rheslip/2HPico-Eurorack-Module-Hardware/Images/IMG_0591.JPG

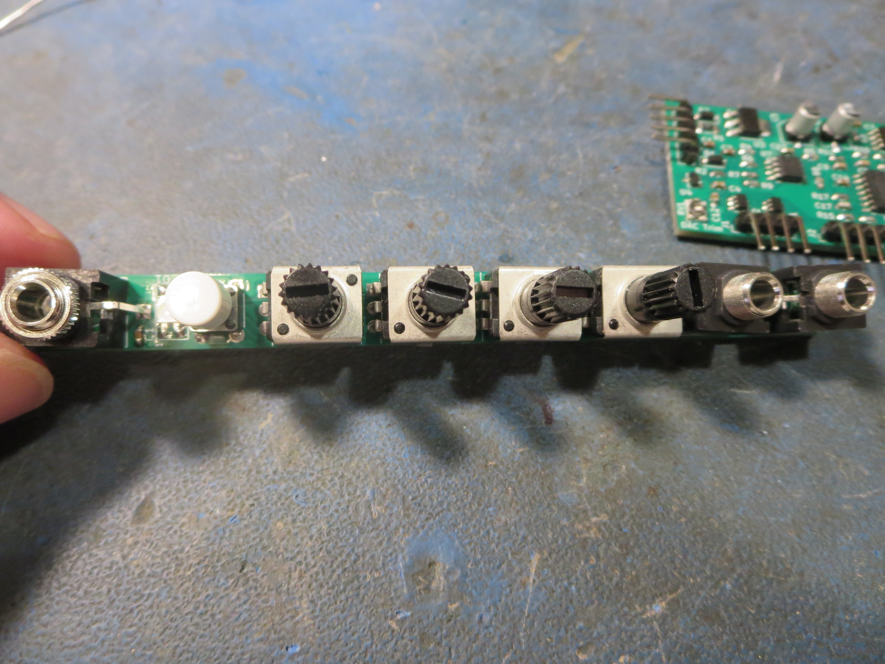
Images/IMG_0591.JPG
