rheslip/2HPico-Eurorack-Module-Hardware/Images/IMG_0592.JPG

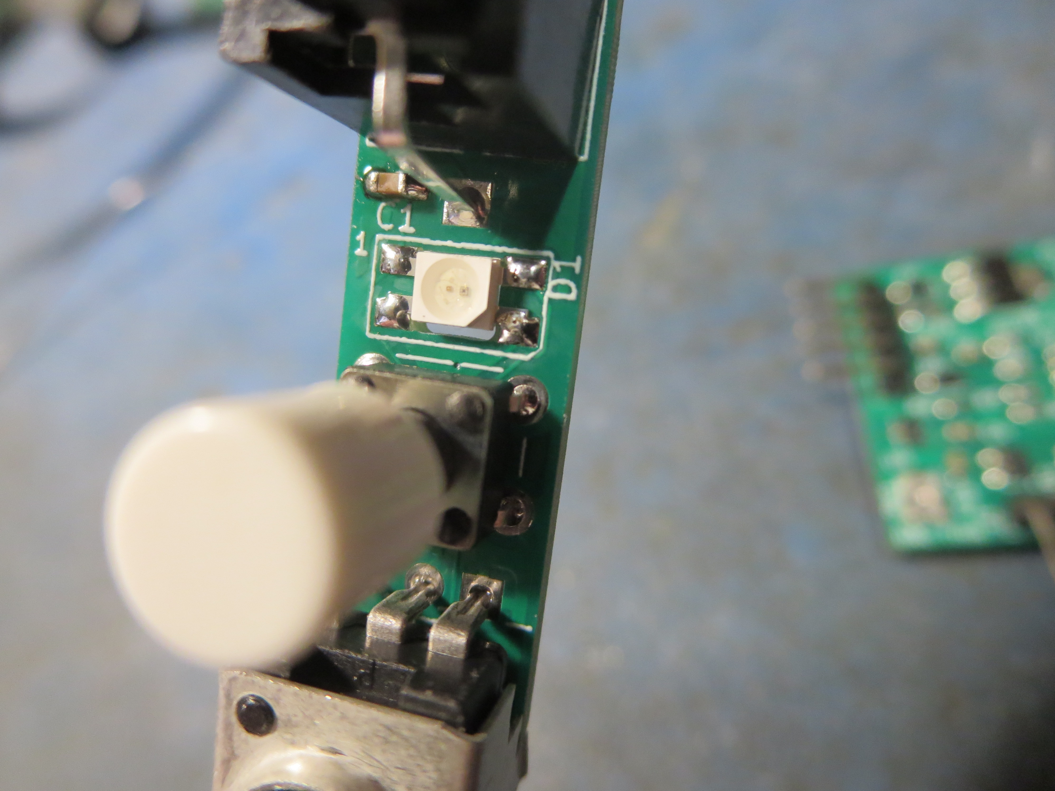
Images/IMG_0592.JPG
