rheslip/2HPico-Eurorack-Module-Hardware/Images/IMG_0594.JPG

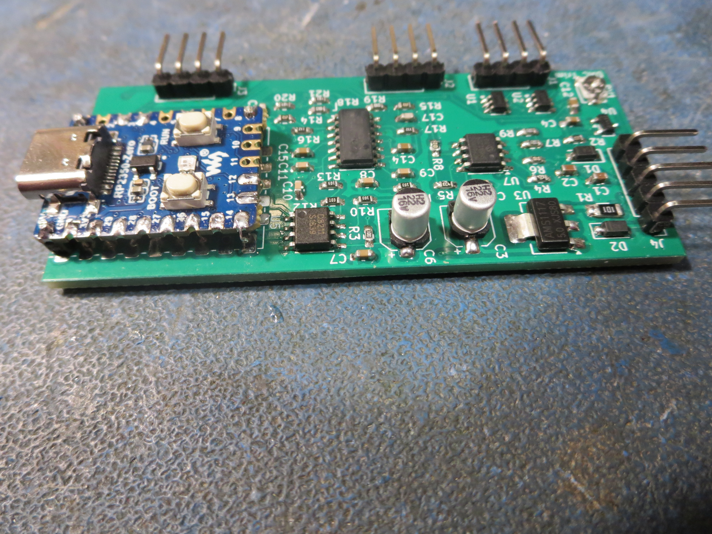
Images/IMG_0594.JPG
