rheslip/2HPico-Eurorack-Module-Hardware/Images/IMG_0597.JPG

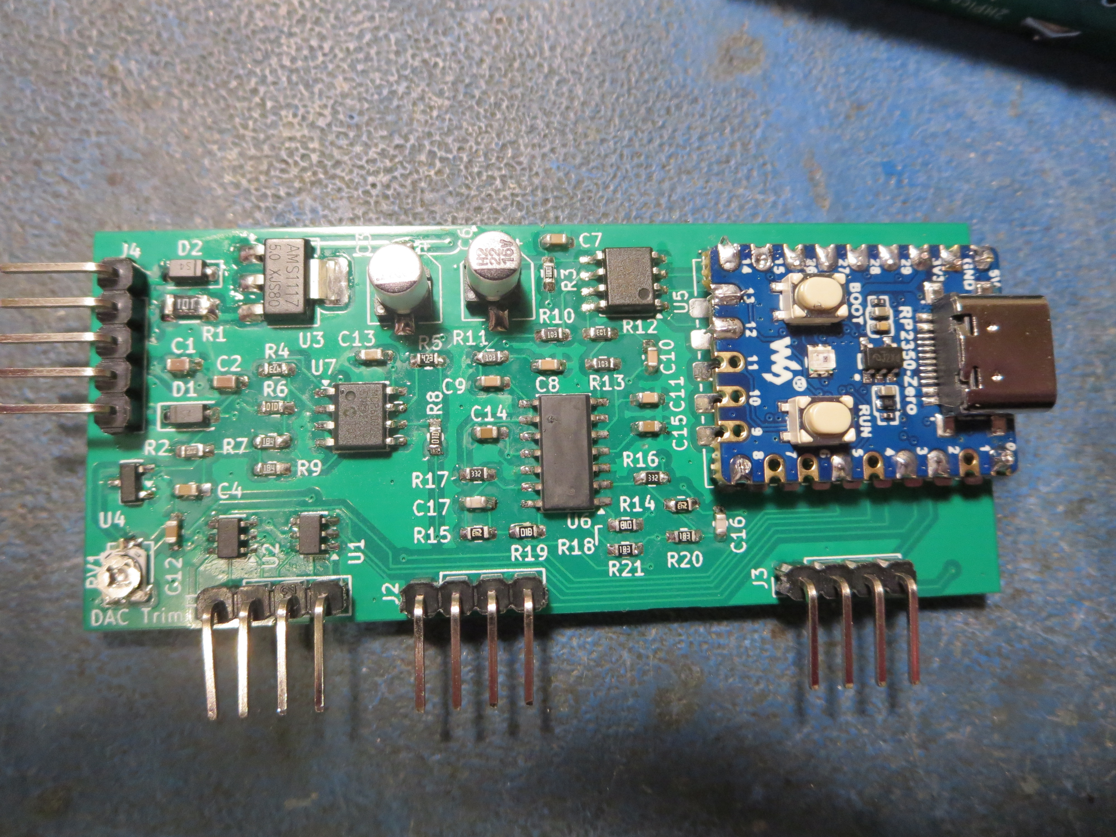
Images/IMG_0597.JPG
