rheslip/2HPico-Eurorack-Module-Hardware/Images/IMG_0598.JPG

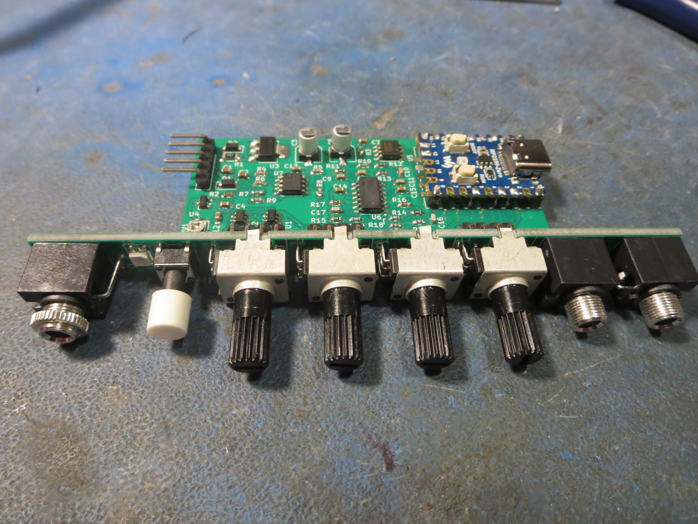
Images/IMG_0598.JPG
