rheslip/2HPico-Eurorack-Module-Hardware/Images/IMG_0600.JPG

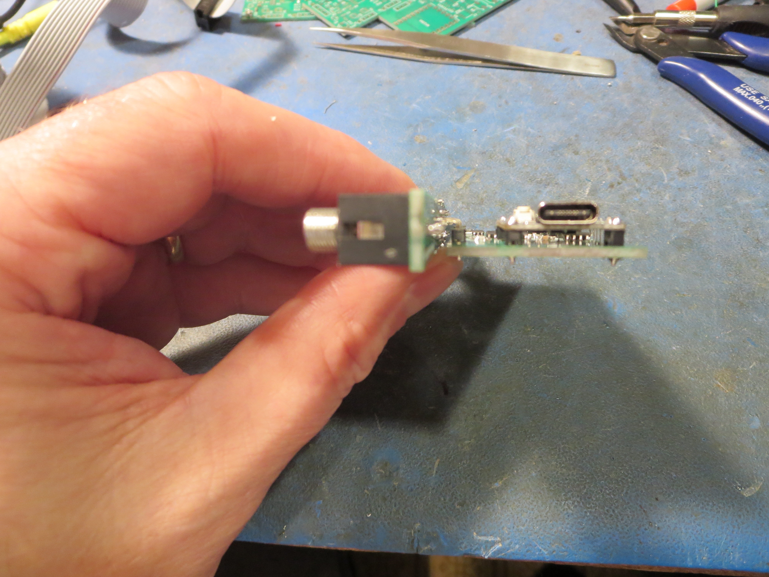
Images/IMG_0600.JPG
