rheslip/2HPico-Eurorack-Module-Hardware/Images/IMG_0606.JPG

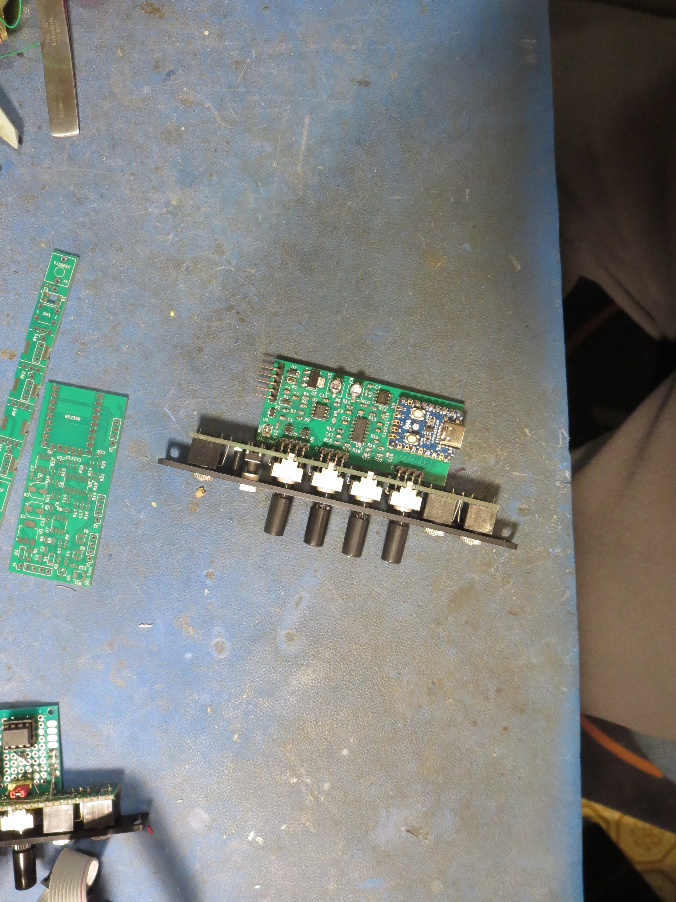
Images/IMG_0606.JPG
